open-thngs/so-dimm-esp32-cm/img/DSC5800.jpg

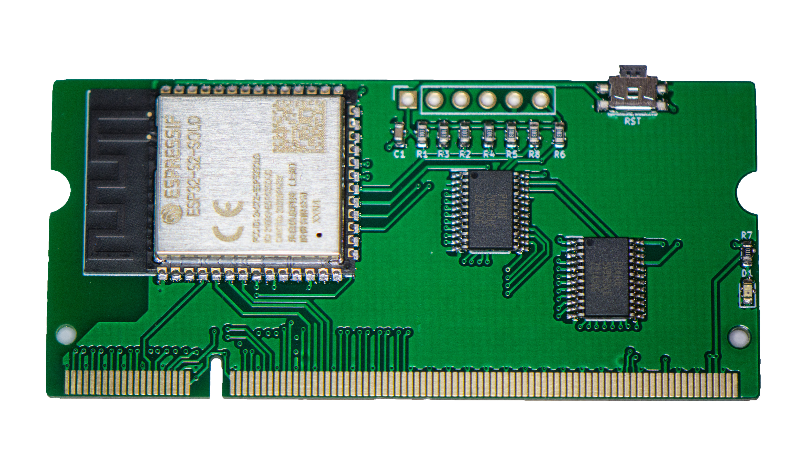
img/DSC5800.jpg
